malcp/small-greenhouse/draws/windowFrameWidth.FCStd

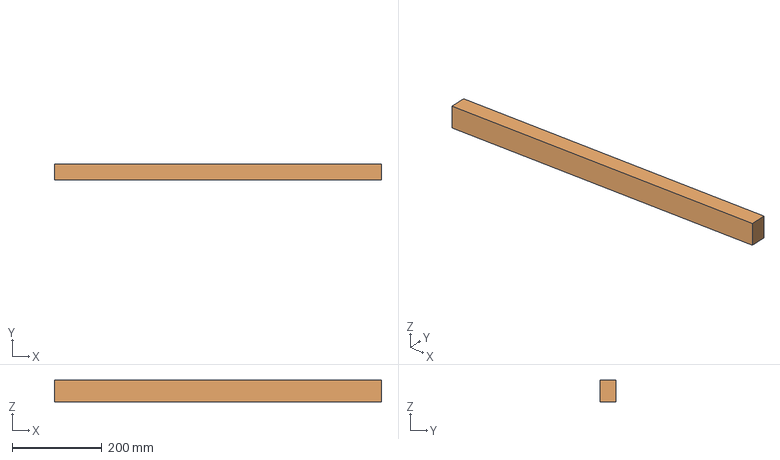
[picture p17: CAD file, 2021-04-11]
draws/windowFrameWidth.FCStd
728.0 x 36.0 x 48.0 mm
