malcp/small-greenhouse/draws/innerHeight.FCStd

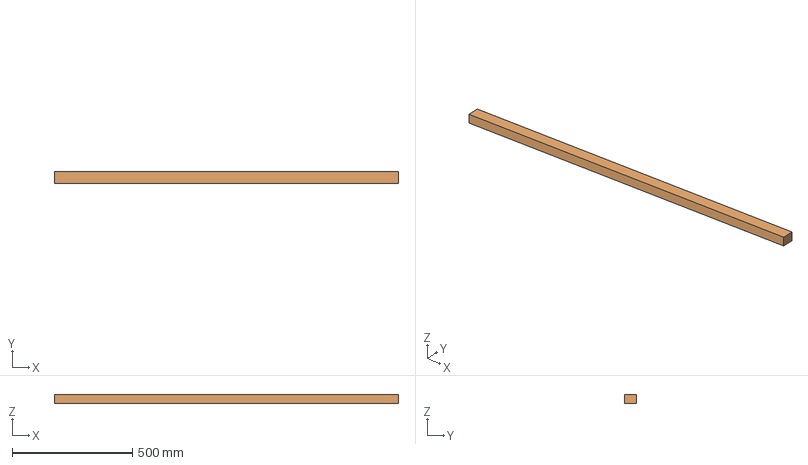
[picture p18: CAD file, 2021-04-11]
draws/innerHeight.FCStd
1428.0 x 48.0 x 36.0 mm
