malcp/small-greenhouse/draws/thinOuterDeep.FCStd

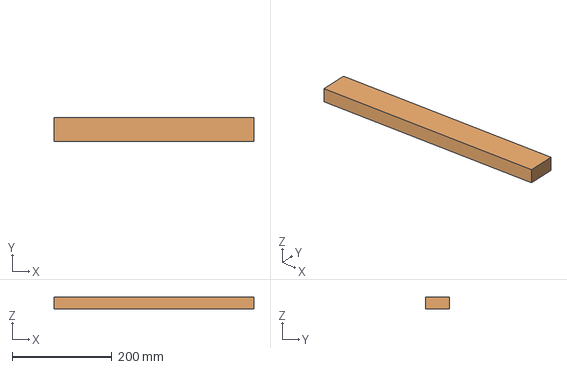
[picture p19: CAD file, 2021-04-11]
draws/thinOuterDeep.FCStd
400.0 x 48.0 x 23.0 mm
