malcp/small-greenhouse/draws/thinInnerWidth.FCStd

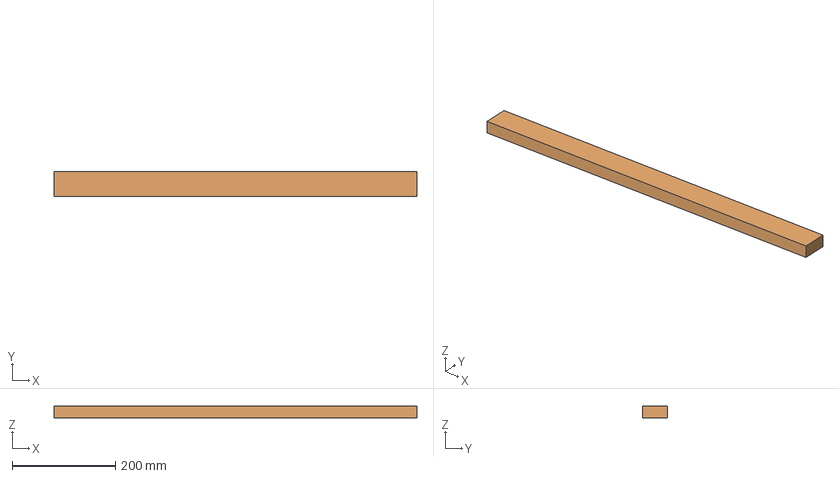
[picture p20: CAD file, 2021-04-11]
draws/thinInnerWidth.FCStd
704.0 x 48.0 x 23.0 mm
