malcp/small-greenhouse/draws/roofHipotenusa.FCStd

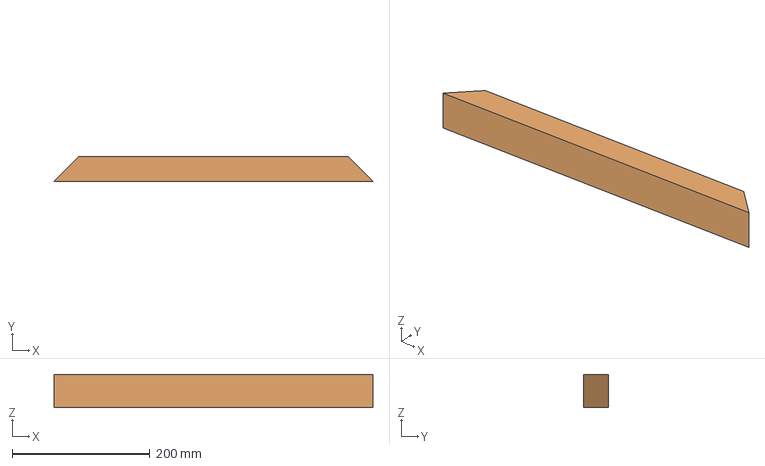
[picture p21: CAD file, 2021-04-11]
draws/roofHipotenusa.FCStd
463.9 x 36.0 x 48.0 mm
