malcp/small-greenhouse/draws/floorDeep.FCStd

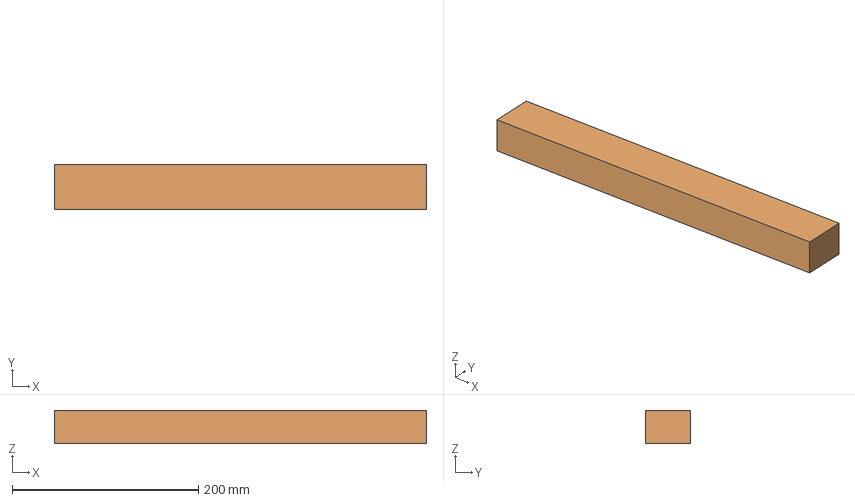
[picture p22: CAD file, 2021-04-11]
draws/floorDeep.FCStd
400.0 x 48.0 x 36.0 mm
