malcp/small-greenhouse/draws/roofBase.FCStd

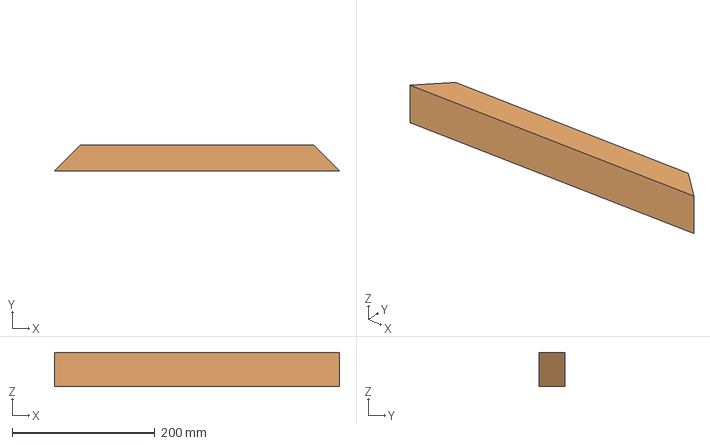
[picture p23: CAD file, 2021-04-11]
draws/roofBase.FCStd
400.0 x 36.0 x 48.0 mm
