malcp/small-greenhouse/draws/thinDoorFrameWidth.FCStd

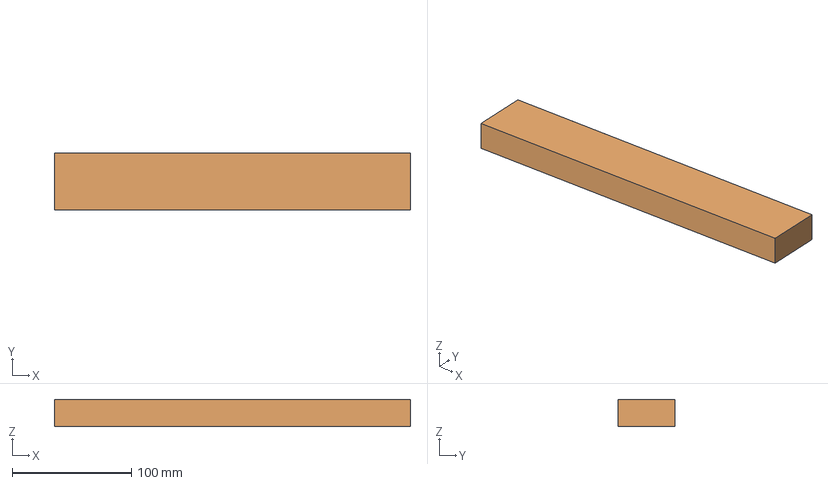
[picture p24: CAD file, 2021-04-11]
draws/thinDoorFrameWidth.FCStd
299.0 x 48.0 x 23.0 mm
