malcp/small-greenhouse/draws/outerDeep.FCStd

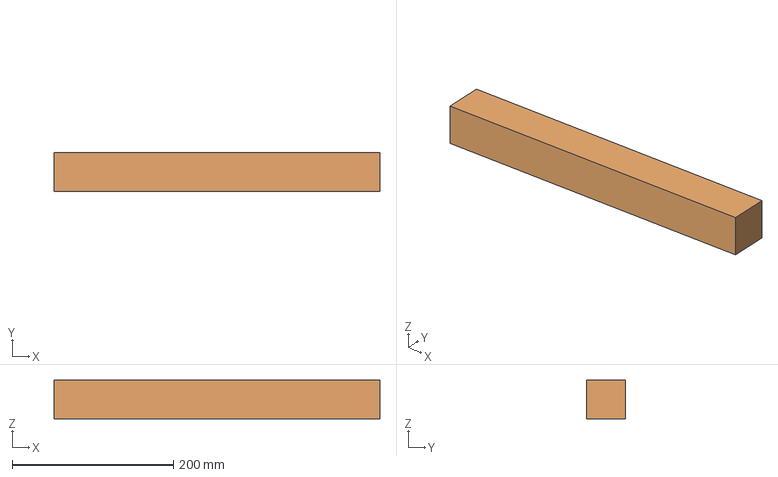
[picture p25: CAD file, 2021-04-05]
draws/outerDeep.FCStd
404.0 x 48.0 x 48.0 mm
